taejun13/HeterogeneousStroke/Sandbox Program/HeterogeneousStroke/img/pattern1.PNG

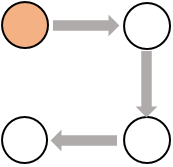
Sandbox Program/HeterogeneousStroke/img/pattern1.PNG
