taejun13/HeterogeneousStroke/Sandbox Program/HeterogeneousStroke/img/pattern2.PNG

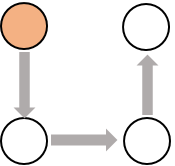
Sandbox Program/HeterogeneousStroke/img/pattern2.PNG
