taejun13/HeterogeneousStroke/Sandbox Program/HeterogeneousStroke/img/pattern4.PNG

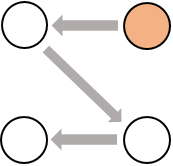
Sandbox Program/HeterogeneousStroke/img/pattern4.PNG
