taejun13/HeterogeneousStroke/Sandbox Program/HeterogeneousStroke/img/pattern5.PNG

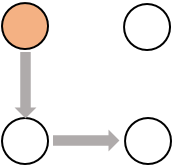
Sandbox Program/HeterogeneousStroke/img/pattern5.PNG
