taejun13/HeterogeneousStroke/Sandbox Program/HeterogeneousStroke/img/pattern8.PNG

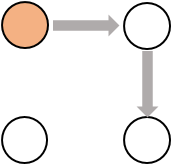
Sandbox Program/HeterogeneousStroke/img/pattern8.PNG
