taejun13/HeterogeneousStroke/Sandbox Program/HeterogeneousStroke/img/pattern9.PNG

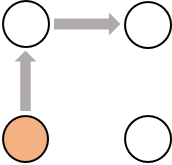
Sandbox Program/HeterogeneousStroke/img/pattern9.PNG
