taejun13/HeterogeneousStroke/Sandbox Program/HeterogeneousStroke/img/pattern10.PNG

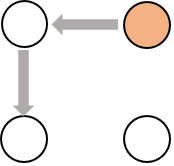
Sandbox Program/HeterogeneousStroke/img/pattern10.PNG
