taejun13/HeterogeneousStroke/Sandbox Program/HeterogeneousStroke/img/pattern11.PNG

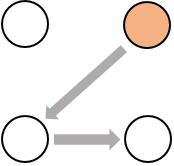
Sandbox Program/HeterogeneousStroke/img/pattern11.PNG
