taejun13/HeterogeneousStroke/Sandbox Program/HeterogeneousStroke/img/pattern26.PNG

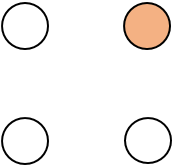
Sandbox Program/HeterogeneousStroke/img/pattern26.PNG
