taejun13/HeterogeneousStroke/Sandbox Program/HeterogeneousStroke/img/pattern27.PNG

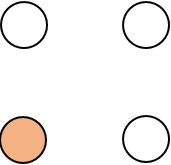
Sandbox Program/HeterogeneousStroke/img/pattern27.PNG
