taejun13/HeterogeneousStroke/Sandbox Program/HeterogeneousStroke/img/pattern28.PNG

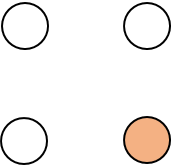
Sandbox Program/HeterogeneousStroke/img/pattern28.PNG
